dickansj/MasterYourPPE/content/trusted-resources/graphs.md

+++
widget = "blank"  # See https://sourcethemes.com/academic/docs/page-builder/
headless = true  # This file represents a page section.
active = true  # Activate this widget? true/false
weight = 10  # Order that this section will appear.

title = ""
subtitle = ""

[design]
  # Choose how many columns the section has. Valid values: 1 or 2.
  columns = "1"

[design.background]
  # Apply a background color, gradient, or image.
  #   Uncomment (by removing `#`) an option to apply it.
  #   Choose a light or dark text color by setting `text_color_light`.
  #   Any HTML color name or Hex value is valid.

  # Background color.
  # color = "navy"
  
  # Background gradient.
  ## gradient_start = "#80CED7"
  ## gradient_end = "#007EA7"
  
  # Background image.
  # image = "image.jpg"  # Name of image in `static/img/`.
  # image_darken = 0.6  # Darken the image? Range 0-1 where 0 is transparent and 1 is opaque.
  # image_size = "cover"  #  Options are `cover` (default), `contain`, or `actual` size.
  # image_position = "center"  # Options include `left`, `center` (default), or `right`.
  # image_parallax = true  # Use a fun parallax-like fixed background effect? true/false
  
  # Text color (true=light or false=dark).
  text_color_light = false

[design.spacing]
  # Customize the section spacing. Order is top, right, bottom, left.
  padding = ["20px", "0", "20px", "0"]

[advanced]
 # Custom CSS. 
 css_style = ""
 
 # CSS class.
 css_class = ""
+++

<div class="container-fluid">
  <div class="row featurette">
    <div class="col-xs-12 col-sm-12 col-md-12 col-lg-12 col-xl-12 section-heading">
      <h1>Coronavirus Resources</h1>
    </div>
  </div>
  <div class="row align-items left">
    <div class="col-xs-12 col-sm-12 col-md-12 col-lg-12 col-xl-12">
      <h3><i class="far fa-chart-bar"></i>&nbsp;Recent Data</h3>
    </div>
  </div>
  <div class="row align-items-center">
    <div class="col-xs-12 col-sm-12 col-md-6 col-lg-6 col-xl-6 mx-auto d-block float-xs-none">
      <iframe src="https://public.domo.com/cards/azrGr" width="100%" height="600" marginheight="0" marginwidth="0" frameborder="0"></iframe>
    </div>
    <div class="col-xs-12 col-sm-12 col-md-6 col-lg-6 col-xl-6 mx-auto d-block float-xs-none">
      <iframe src="https://public.domo.com/cards/dyqEV" width="100%" height="600" marginheight="0" marginwidth="0" frameborder="0"></iframe>
    </div>
  </div>
  <div class="row align-items-center">
    <div class="col-xs-12 col-sm-12 col-md-6 col-lg-6 col-xl-6 mx-auto d-block float-xs-none">
      <iframe src="https://public.domo.com/cards/aAR5B" width="100%" height="600" marginheight="0" marginwidth="0" frameborder="0"></iframe>
    </div>
    <div class="col-xs-12 col-sm-12 col-md-6 col-lg-6 col-xl-6 mx-auto d-block float-xs-none">
      <iframe src="https://public.domo.com/cards/dJ45D" width="100%" height="600" marginheight="0" marginwidth="0" frameborder="0"></iframe>
    </div>
  </div>
  <div class="row align-items-center">
    <div class="col-xs-12 col-sm-12 col-md-6 col-lg-6 col-xl-6 mx-auto d-block float-xs-none">
      <iframe src="https://public.domo.com/cards/dG1jy" width="100%" height="600" marginheight="0" marginwidth="0" frameborder="0"></iframe>
    </div>
    <div class="col-xs-12 col-sm-12 col-md-6 col-lg-6 col-xl-6 mx-auto d-block float-xs-none">
      <iframe src="https://public.domo.com/cards/aKg4r" width="100%" height="600" marginheight="0" marginwidth="0" frameborder="0"></iframe>
    </div>
  </div>
</div>
