dickansj/MasterYourPPE/assets/images/news/covid-healthcare.png

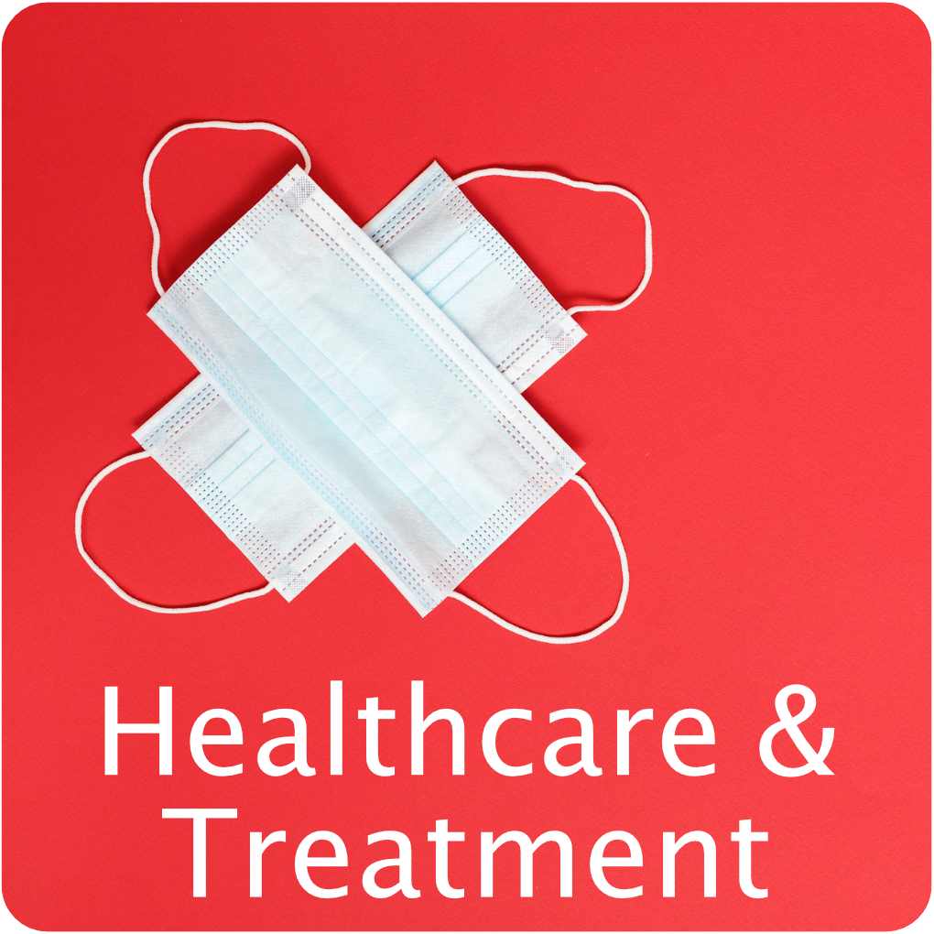
assets/images/news/covid-healthcare.png
