dickansj/MasterYourPPE/assets/images/news/who-dashboard512-crunch.png

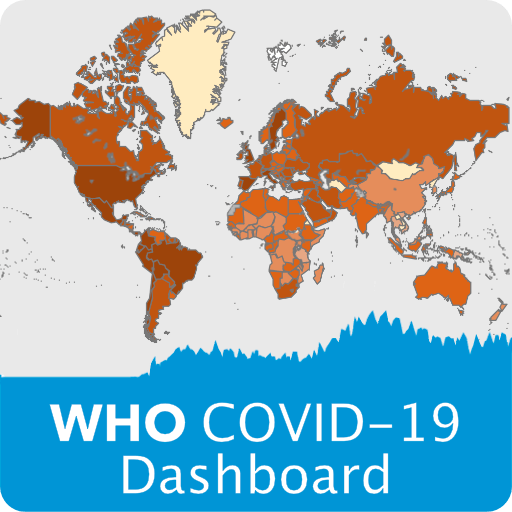
assets/images/news/who-dashboard512-crunch.png
