dickansj/MasterYourPPE/assets/images/team/MTrivedi.jpg

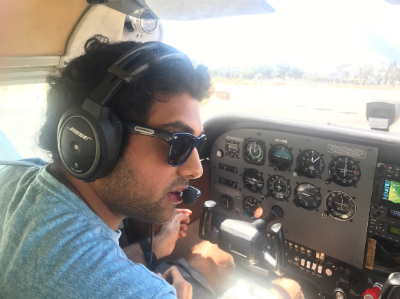
assets/images/team/MTrivedi.jpg
