dickansj/MasterYourPPE/assets/images/team/Shinozaki.jpg

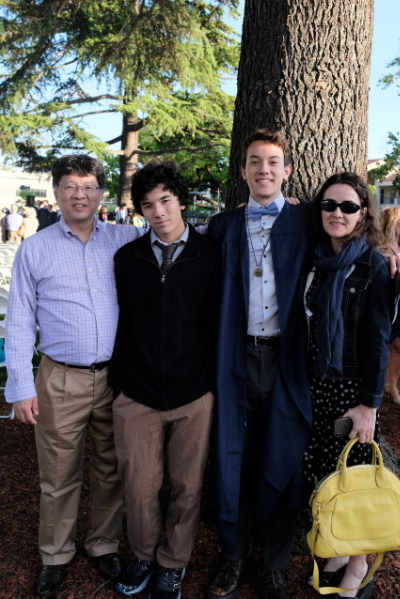
assets/images/team/Shinozaki.jpg
