dickansj/MasterYourPPE/assets/images/team/Stefanescu.jpg

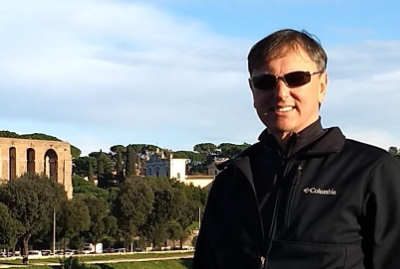
assets/images/team/Stefanescu.jpg
