dickansj/MasterYourPPE/assets/images/tips/clip-crunch.png

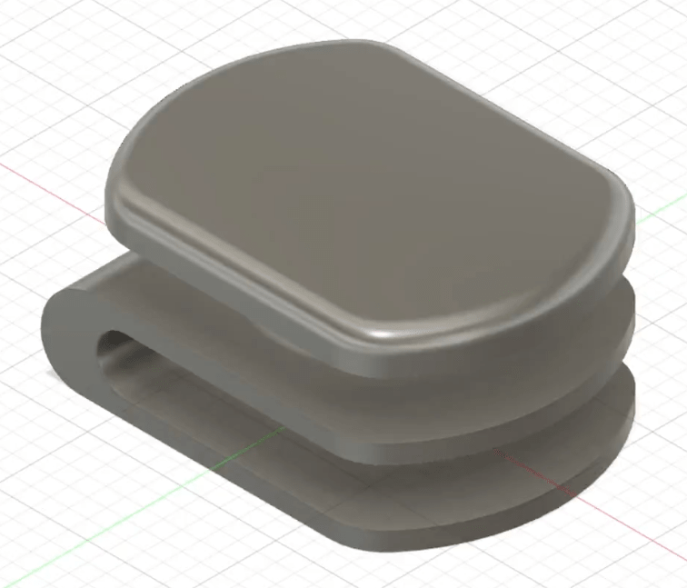
assets/images/tips/clip-crunch.png
