dickansj/MasterYourPPE/assets/images/tips/clip-transparent-crunch.png

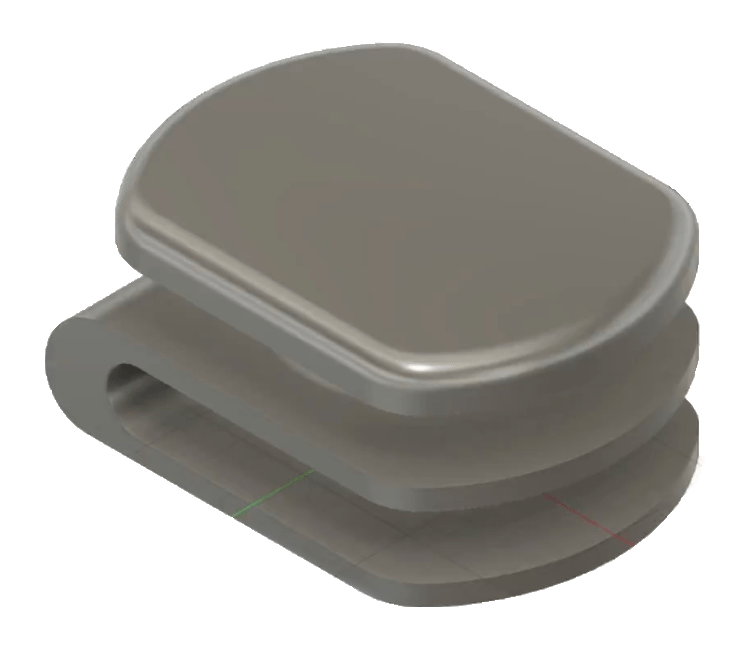
assets/images/tips/clip-transparent-crunch.png
