dickansj/MasterYourPPE/assets/images/tips/clip.png

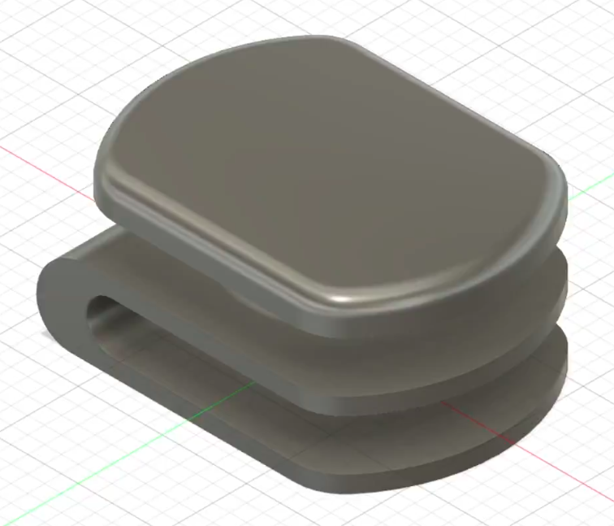
assets/images/tips/clip.png
