dickansj/MasterYourPPE/assets/images/tips/maskframevid-crunch.png

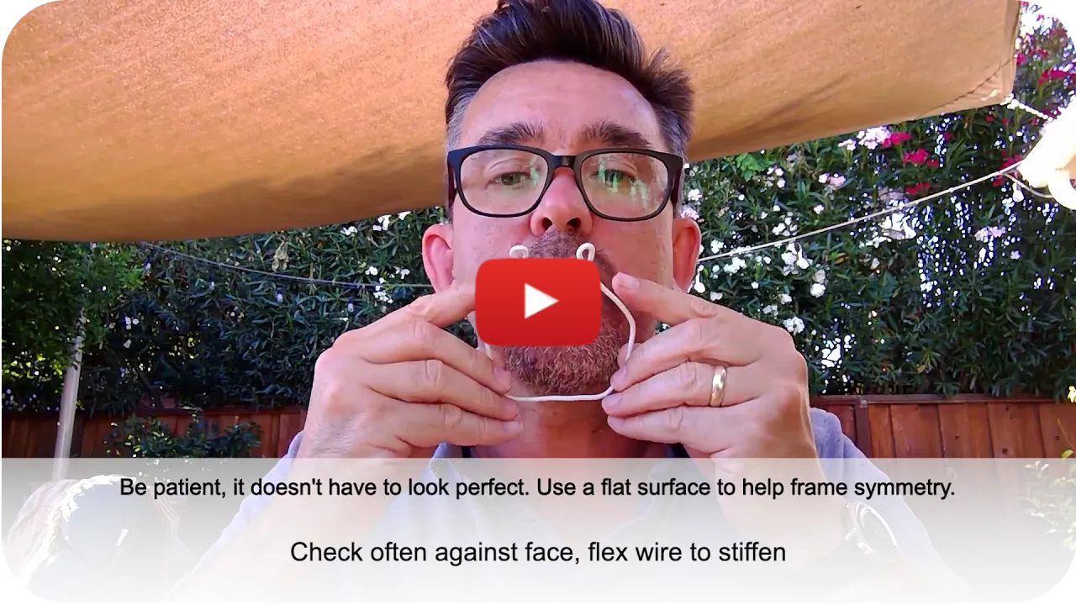
assets/images/tips/maskframevid-crunch.png
