dickansj/MasterYourPPE/assets/wiki/frame-side-view-crunch.png

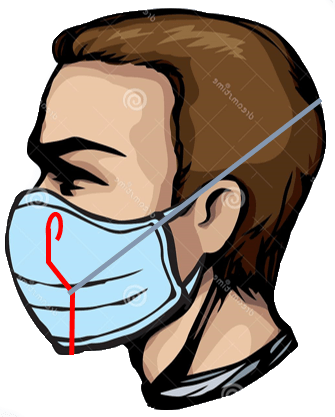
assets/wiki/frame-side-view-crunch.png
